asairamyasri/ESDP-Project-Smart-Watch/Images/Bottom_Case.png

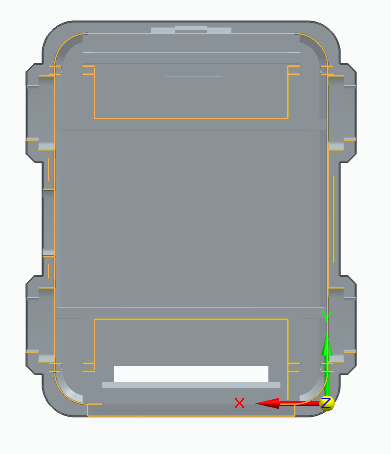
Images/Bottom_Case.png
