asairamyasri/ESDP-Project-Smart-Watch/Images/Button.png

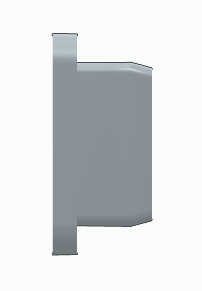
Images/Button.png
